iollama/Voice-Assistant-5/personas/Historical/Alexander Hamilton/concerned.jpg

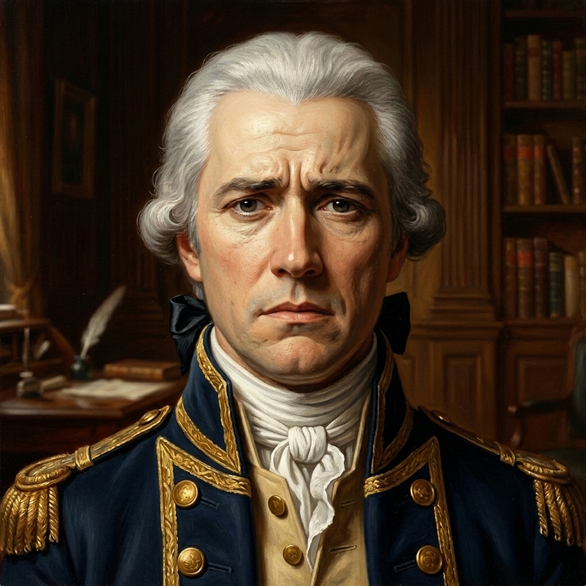
personas/Historical/Alexander Hamilton/concerned.jpg
