iollama/Voice-Assistant-5/personas/Historical/Alexander Hamilton/confused.jpg

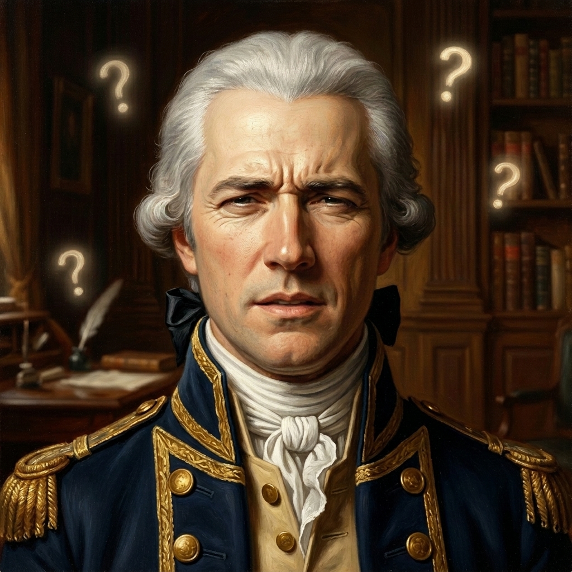
personas/Historical/Alexander Hamilton/confused.jpg
