iollama/Voice-Assistant-5/personas/Historical/Alexander Hamilton/excited.jpg

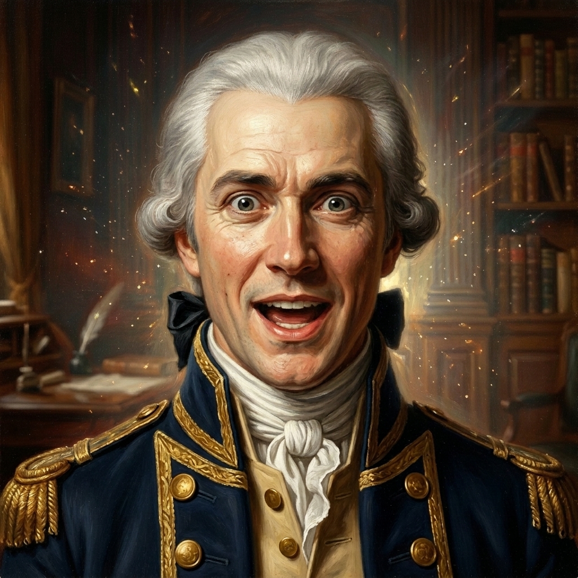
personas/Historical/Alexander Hamilton/excited.jpg
