iollama/Voice-Assistant-5/personas/Historical/Theodor Herzl/concerned.jpg

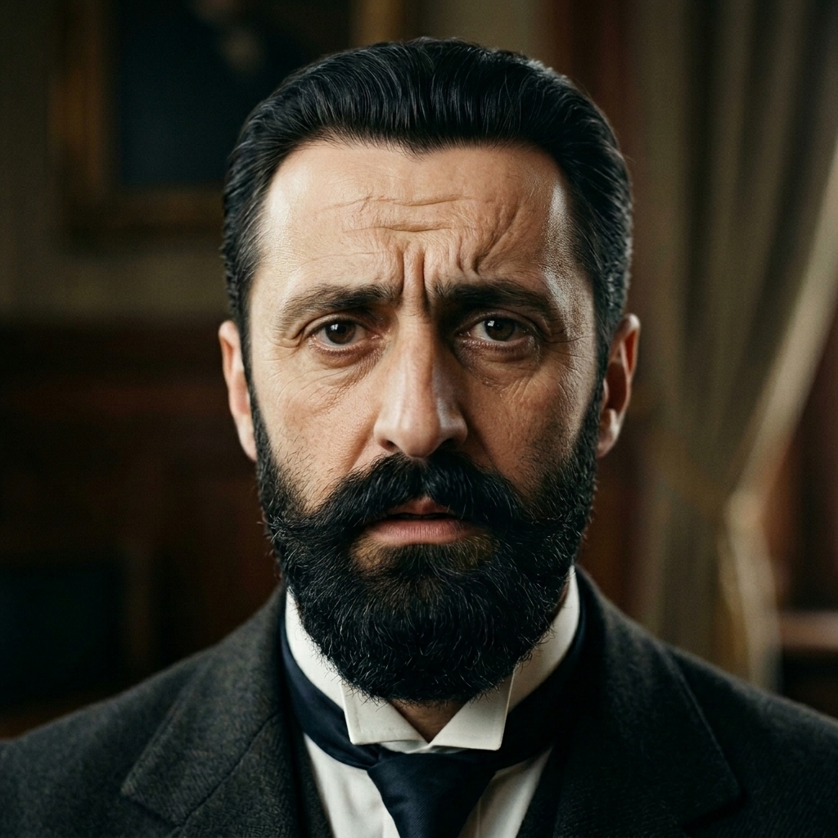
personas/Historical/Theodor Herzl/concerned.jpg
