iollama/Voice-Assistant-5/personas/Historical/Theodor Herzl/confused.jpg

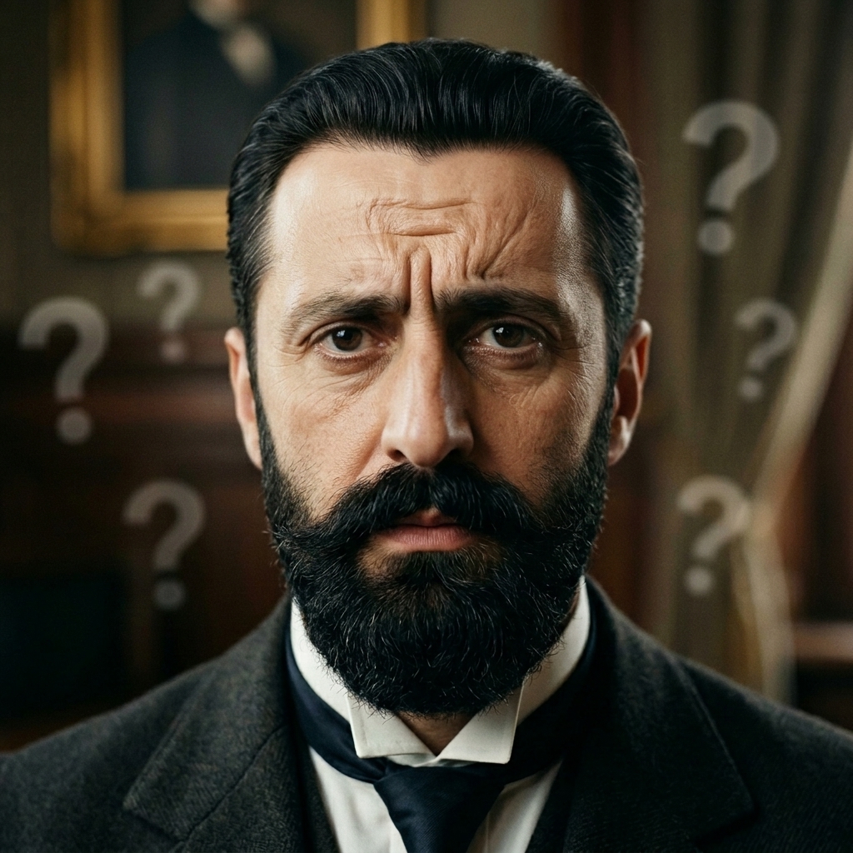
personas/Historical/Theodor Herzl/confused.jpg
