iollama/Voice-Assistant-5/personas/Historical/Theodor Herzl/excited.jpg

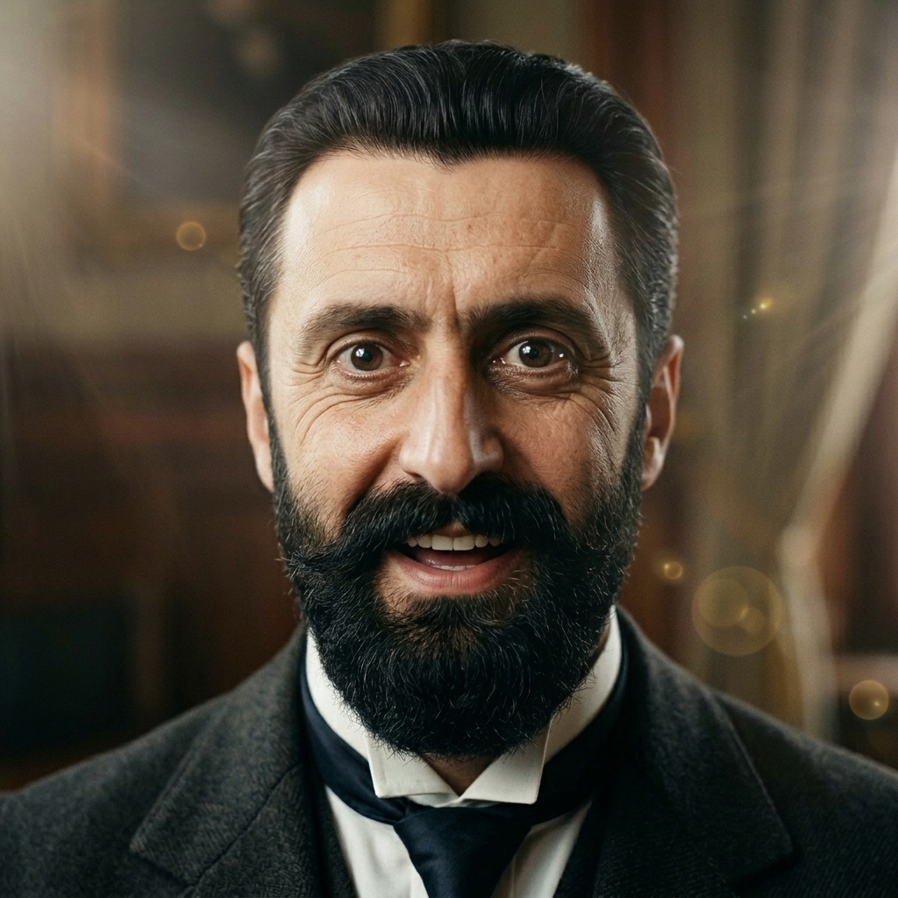
personas/Historical/Theodor Herzl/excited.jpg
