iollama/Voice-Assistant-5/voice_agent_5/utils/preview/confused.gif

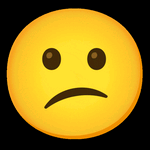
voice_agent_5/utils/preview/confused.gif
