iollama/Voice-Assistant-5/voice_agent_5/utils/preview/empathetic.gif

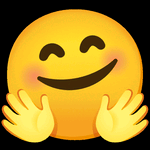
voice_agent_5/utils/preview/empathetic.gif
