iollama/Voice-Assistant-5/voice_agent_5/utils/preview/excited.gif

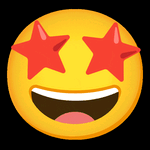
voice_agent_5/utils/preview/excited.gif
