iollama/Voice-Assistant-5/voice_agent_5/utils/preview/neutral.gif

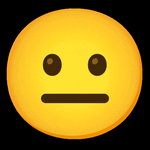
voice_agent_5/utils/preview/neutral.gif
