iollama/Voice-Assistant-5/voice_agent_5/webserver.ino

// =====================================================================
// NVS Config & WebServer Handlers
// =====================================================================

// Reads every persisted setting into RAM. Callable at boot (single-threaded)
// and from /restoreAgent (Core 1, with the protocol task live), so the three
// mutex-protected globals are assigned under agent_config_lock().
void load_agent_config() {
  preferences.begin("agentConfig", true);

  size_t blob_len = preferences.getBytesLength("sysPrompt");
  bool needs_sysprompt_migration = false;
  String loaded_prompt;
  if (blob_len > 0) {
    char* buf = (char*)malloc(blob_len + 1);
    preferences.getBytes("sysPrompt", buf, blob_len);
    buf[blob_len] = '\0';
    loaded_prompt = String(buf);
    free(buf);
  } else {
    String legacy = preferences.getString("sysPrompt", "");
    if (legacy.length() > 0) {
      loaded_prompt = legacy;
      needs_sysprompt_migration = true;
    } else {
      loaded_prompt = DEFAULT_SYS_INSTRUCTION;
    }
  }

  g_temperature = preferences.getFloat("temp", DEFAULT_TEMPERATURE);
  g_persist_conversation = preferences.getBool("persist", DEFAULT_PERSIST_CONVO);
  g_verbose_logging = preferences.getBool("verbose", DEFAULT_VERBOSE_LOGGING);
  g_show_hidden_personas = preferences.getBool("showHidden", DEFAULT_SHOW_HIDDEN);
  g_api_key = preferences.getString("apiKey", "");
  g_volume = preferences.getInt("volume", 50);
  if (g_volume < 0) g_volume = 0;
  if (g_volume > 100) g_volume = 100;
  g_audio_output = preferences.getUChar("audioOut", AUDIO_OUT_SPEAKER);
  if (g_audio_output > AUDIO_OUT_HEADPHONES) g_audio_output = AUDIO_OUT_SPEAKER;
  String loaded_voice = preferences.getString("voice", DEFAULT_VOICE);
  if (!voice_is_allowed(loaded_voice)) {
    CPRINTF("NVS: stored voice '%s' not in whitelist, falling back to '%s'\n",
            loaded_voice.c_str(), DEFAULT_VOICE);
    loaded_voice = DEFAULT_VOICE;
  }
  String loaded_language = preferences.getString("lang", DEFAULT_LANGUAGE);
  if (!language_is_allowed(loaded_language)) {
    CPRINTF("NVS: stored language '%s' not in whitelist, falling back to '%s'\n",
            loaded_language.c_str(), DEFAULT_LANGUAGE);
    loaded_language = DEFAULT_LANGUAGE;
  }
  preferences.end();

  agent_config_lock();
  g_sys_instruction = loaded_prompt;
  g_voice           = loaded_voice;
  g_language        = loaded_language;
  agent_config_unlock();

  if (needs_sysprompt_migration) {
    // The blob has to replace the string under the same key, so the remove
    // comes first — which means a failed putBytes would leave NOTHING stored
    // and the next boot would come up on DEFAULT_SYS_INSTRUCTION. Put the
    // legacy string back rather than losing the user's persona.
    preferences.begin("agentConfig", false);
    preferences.remove("sysPrompt");
    size_t written = preferences.putBytes("sysPrompt", loaded_prompt.c_str(),
                                          loaded_prompt.length());
    bool ok = (written == loaded_prompt.length());
    if (!ok) {
      preferences.remove("sysPrompt");
      bool restored = (preferences.putString("sysPrompt", loaded_prompt) > 0);
      CPRINTF("NVS: sysPrompt migration FAILED (wrote %u of %u bytes) — "
              "NVS is full; legacy string %s\n",
              (unsigned)written, (unsigned)loaded_prompt.length(),
              restored ? "restored, will retry next boot" : "COULD NOT BE RESTORED");
    }
    preferences.end();
    if (ok) {
      CPRINTF("NVS: migrated sysPrompt from string to blob (%u bytes)\n",
              (unsigned)loaded_prompt.length());
    }
  }
}

// Main settings page HTML/CSS/JS lives in root_page.h (static PROGMEM), served
// verbatim. Live values are delivered separately via GET /api/config; saves use
// the existing form-POST handlers below. Kept in a .h for the same reason as
// emojis_page.h (Arduino auto-prototyper chokes on embedded JS in .ino files).
#include "root_page.h"
void handle_root() {
  server.sendHeader("Cache-Control", "no-cache");
  server.send_P(200, "text/html; charset=utf-8", ROOT_PAGE_HTML);
}

// Shared idle gate for portal actions that are slow or disruptive.
// server.handleClient() runs on Core 1 alongside captureMicrophone() and
// manageSpeaker(), so a handler that occupies Core 1 for any length of time
// underruns the speaker DMA or drops mic audio. Every such endpoint refuses with
// HTTP 409 mid-turn. Cheap reads don't need the gate.
static bool assistant_in_turn() {
  AssistantState s = (AssistantState)g_state;
  return s == STATE_RECORDING || s == STATE_THINKING || s == STATE_SPEAKING;
}

// Sends the 409 and returns true when the caller should stop.
static bool reject_if_busy() {
  if (!assistant_in_turn()) return false;
  server.send(409, "text/plain", "Busy - try again after the current response.");
  return true;
}

// Escape a string for safe embedding inside a JSON double-quoted value.
static String json_escape(const String& in) {
  String out;
  out.reserve(in.length() + 8);
  for (size_t i = 0; i < in.length(); i++) {
    char c = in[i];
    switch (c) {
      case '"':  out += "\\\""; break;
      case '\\': out += "\\\\"; break;
      case '\n': out += "\\n";  break;
      case '\r': out += "\\r";  break;
      case '\t': out += "\\t";  break;
      default:
        if ((uint8_t)c < 0x20) {
          char buf[7];
          snprintf(buf, sizeof(buf), "\\u%04x", (unsigned)(uint8_t)c);
          out += buf;
        } else {
          out += c;
        }
    }
  }
  return out;
}

// ---- GET /api/config -------------------------------------------------
// Current settings for the static main page to populate itself with.
// Never returns the API key itself — only whether a custom key is set.
void handle_config() {
  // Snapshot the mutex-protected trio into locals first — never hold the lock
  // across the JSON building below.
  String cfg_prompt, cfg_voice, cfg_language;
  agent_config_snapshot(cfg_prompt, cfg_voice, cfg_language);

  String json = "{";
  json += "\"sysPrompt\":\"" + json_escape(cfg_prompt) + "\",";
  json += "\"voice\":\"" + json_escape(cfg_voice) + "\",";
  json += "\"voices\":[";
  for (size_t i = 0; i < VOICE_OPTIONS_COUNT; ++i) {
    if (i) json += ",";
    json += "{\"id\":\"" + String(VOICE_OPTIONS[i].id) + "\",";
    json += "\"label\":\"" + json_escape(VOICE_OPTIONS[i].label) + "\"}";
  }
  json += "],";
  json += "\"language\":\"" + json_escape(cfg_language) + "\",";
  json += "\"languages\":[";
  for (size_t i = 0; i < LANGUAGE_OPTIONS_COUNT; ++i) {
    if (i) json += ",";
    json += "{\"id\":\"" + String(LANGUAGE_OPTIONS[i].id) + "\",";
    json += "\"label\":\"" + json_escape(LANGUAGE_OPTIONS[i].label) + "\"}";
  }
  json += "],";
  json += "\"persist\":"  + String(g_persist_conversation ? "true" : "false") + ",";
  json += "\"verbose\":"  + String(g_verbose_logging ? "true" : "false") + ",";
  json += "\"showHidden\":" + String(g_show_hidden_personas ? "true" : "false") + ",";
  json += "\"volume\":"   + String((int)g_volume) + ",";
  json += "\"audioOut\":" + String((int)g_audio_output) + ",";
  // LittleFS storage budget — the portal's "Provision default persona" preflight checks
  // the decoded frame total against fsFree before writing anything to /default.
  json += "\"fsTotal\":" + String((uint32_t)LittleFS.totalBytes()) + ",";
  json += "\"fsFree\":"  + String((uint32_t)(LittleFS.totalBytes() - LittleFS.usedBytes())) + ",";
  json += "\"apiKeySet\":" + String(g_api_key.length() > 0 ? "true" : "false") + ",";
  json += "\"apMode\":"   + String(ap_mode ? "true" : "false") + ",";
  json += "\"ssid\":\""   + json_escape(ap_mode ? WiFi.softAPSSID() : WiFi.SSID()) + "\",";
#if USE_DISPLAY
  json += "\"useDisplay\":true,";
#else
  json += "\"useDisplay\":false,";
#endif
  json += "\"tokens\":{";
  json += "\"total\":"       + String((uint32_t)g_tokens.total);
  json += ",\"input\":"      + String((uint32_t)g_tokens.input);
  json += ",\"inputCached\":" + String((uint32_t)g_tokens.input_cached);
  json += ",\"inputText\":"  + String((uint32_t)g_tokens.input_text);
  json += ",\"inputAudio\":" + String((uint32_t)g_tokens.input_audio);
  json += ",\"output\":"     + String((uint32_t)g_tokens.output);
  json += ",\"outputText\":" + String((uint32_t)g_tokens.output_text);
  json += ",\"outputAudio\":" + String((uint32_t)g_tokens.output_audio);
  json += "}}";
  server.sendHeader("Cache-Control", "no-cache");
  server.send(200, "application/json", json);
}

// =====================================================================
// WI-FI NETWORK API
// =====================================================================
// Up to WIFI_MAX_NETWORKS saved networks; the store itself lives in wifi_store.h
// and is persisted by wifi_store_persist() in wifi.ino.
//
// NO ROUTE HERE EVER RETURNS A STORED PASSWORD. Passwords go in and are never
// readable back out — that property is what makes the (currently plaintext) NVS
// blob acceptable, and it must survive any change to these handlers.

// wifi_store_remove() compacts the array, so a cached slot index goes stale after
// any deletion. Re-derive it from the SSID we are actually associated with.
static void wifi_refresh_active_slot() {
  g_wifi_active_slot = ap_mode ? -1 : wifi_store_find(g_wifi_store, WiFi.SSID().c_str());
}

// Saved networks, most recently used first — the same order the boot cascade tries.
static String wifi_nets_json() {
  String json = "{";
  json += "\"max\":"    + String(WIFI_MAX_NETWORKS) + ",";
  json += "\"count\":"  + String((int)g_wifi_store.count) + ",";
  json += "\"apMode\":" + String(ap_mode ? "true" : "false") + ",";
  json += "\"nets\":[";
  uint8_t order[WIFI_MAX_NETWORKS];
  int n = wifi_store_order_by_recency(g_wifi_store, order);
  for (int i = 0; i < n; i++) {
    const WifiNet& net = g_wifi_store.nets[order[i]];
    if (i) json += ",";
    json += "{\"ssid\":\""   + json_escape(net.ssid) + "\"";
    json += ",\"lastUsed\":"  + String((uint32_t)net.last_epoch);
    json += ",\"neverUsed\":" + String(net.use_seq == 0 ? "true" : "false");
    json += ",\"active\":"    + String((!ap_mode && (int)order[i] == g_wifi_active_slot)
                                       ? "true" : "false");
    json += "}";
  }
  json += "],";
  // Outcome of an explicit Connect request, if one was made before this boot. The
  // page uses it to report a target it could not reach, since the reboot destroys
  // the request's own HTTP response.
  json += "\"lastAttempt\":";
  if (g_wifi_request_ssid.length() > 0) {
    json += "{\"ssid\":\"" + json_escape(g_wifi_request_ssid) + "\",\"ok\":";
    json += g_wifi_request_ok ? "true" : "false";
    json += "}";
  } else {
    json += "null";
  }
  json += "}";
  return json;
}

// ---- GET /api/wifi ---------------------------------------------------
void handle_wifi_list() {
  server.sendHeader("Cache-Control", "no-cache");
  server.send(200, "application/json", wifi_nets_json());
}

// ---- GET /api/wifi/scan ----------------------------------------------
// Asynchronous by necessity. WiFi.scanNetworks() blocks for 2-4 s, and this
// handler runs on Core 1 inside server.handleClient() — blocking there would
// starve the audio loop. So: the first call kicks off a background scan and
// answers {"status":"scanning"}; the page polls until the results are ready.
// The boot cascade is the one place a blocking scan is legitimate, because it
// runs in setup() before loop() and the protocol task exist.
void handle_wifi_scan() {
  if (reject_if_busy()) return;

  // Tracks whether the poll sequence we are in has already started a scan, so a
  // fresh press of Scan never answers with leftovers from an abandoned earlier
  // one. (A request abandoned mid-scan can still yield one stale list on the next
  // press; harmless, since saving a network that is not currently in range is a
  // supported action anyway.)
  static bool scan_started = false;

  int16_t n = WiFi.scanComplete();

  if (!scan_started) {
    if (n >= 0) WiFi.scanDelete();     // discard results nobody collected
    WiFi.scanNetworks(true);
    scan_started = true;
    server.send(200, "application/json", "{\"status\":\"scanning\"}");
    return;
  }
  if (n == WIFI_SCAN_RUNNING) {
    server.send(200, "application/json", "{\"status\":\"scanning\"}");
    return;
  }
  if (n < 0) {
    scan_started = false;              // let the next press try again
    server.send(500, "text/plain", "Scan failed");
    return;
  }

  const int SCAN_MAX = 64;
  if (n > SCAN_MAX) n = SCAN_MAX;

  // Sort indices by RSSI descending, so the dedup below keeps the strongest BSSID
  // for each SSID and the page lists the nearest networks first.
  int idx[SCAN_MAX];
  for (int i = 0; i < n; i++) idx[i] = i;
  for (int i = 1; i < n; i++) {
    int key = idx[i];
    int j = i - 1;
    while (j >= 0 && WiFi.RSSI(idx[j]) < WiFi.RSSI(key)) { idx[j + 1] = idx[j]; j--; }
    idx[j + 1] = key;
  }

  // Pull each SSID out once. WiFi.SSID(int) builds a String per call, and the
  // dedup below is O(n^2) — calling it inside the inner loop would mean up to
  // ~2000 transient heap allocations on Core 1, which is the churn the
  // no-heap-on-the-audio-path rule exists to avoid even though this is off it.
  String ssids[SCAN_MAX];
  for (int i = 0; i < n; i++) ssids[i] = WiFi.SSID(idx[i]);

  String json = "{\"status\":\"done\",\"nets\":[";
  int emitted = 0;
  for (int i = 0; i < n; i++) {
    const String& ssid = ssids[i];
    if (ssid.length() == 0) continue;   // hidden SSID — nothing to offer the user
    bool dup = false;
    for (int j = 0; j < i; j++) {
      if (ssids[j] == ssid) { dup = true; break; }   // sorted by RSSI, so [j] is the stronger
    }
    if (dup) continue;
    if (emitted) json += ",";
    json += "{\"ssid\":\"" + json_escape(ssid) + "\"";
    json += ",\"rssi\":"   + String((int)WiFi.RSSI(idx[i]));
    json += ",\"secure\":" + String(WiFi.encryptionType(idx[i]) != WIFI_AUTH_OPEN
                                    ? "true" : "false");
    json += ",\"saved\":"  + String(wifi_store_find(g_wifi_store, ssid.c_str()) >= 0
                                    ? "true" : "false");
    json += "}";
    emitted++;
  }
  json += "]}";

  WiFi.scanDelete();
  scan_started = false;
  server.sendHeader("Cache-Control", "no-cache");
  server.send(200, "application/json", json);
}

// ---- POST /api/wifi/add ----------------------------------------------
// Adds a network, or replaces the password of one already saved. No reboot and
// no change to the current connection — pre-loading a network you are nowhere
// near is the point. The response says exactly what happened (including which
// entry was evicted to make room) so the page can report it.
void handle_wifi_add() {
  if (reject_if_busy()) return;

  String ssid = server.arg("ssid");
  String pass = server.arg("pass");
  if (ssid.length() == 0) {
    server.send(400, "text/plain", "SSID required");
    return;
  }
  if (ssid.length() >= WIFI_SSID_MAX) {
    server.send(400, "text/plain", "SSID too long (max 32 characters)");
    return;
  }
  if (pass.length() >= WIFI_PASS_MAX) {
    server.send(400, "text/plain", "Password too long (max 63 characters)");
    return;
  }

  bool updated = wifi_store_find(g_wifi_store, ssid.c_str()) >= 0;
  char evicted[WIFI_SSID_MAX];
  int slot = wifi_store_upsert(g_wifi_store, ssid.c_str(), pass.c_str(), evicted);
  if (slot < 0) {
    server.send(400, "text/plain", "Could not save that network");
    return;
  }
  if (!wifi_store_persist()) {
    server.send(500, "text/plain",
                "Settings storage is full — the network was not saved.");
    return;
  }
  wifi_refresh_active_slot();

  CPRINTF("Wi-Fi store: %s '%s' in slot %d%s%s\n",
          updated ? "updated" : "added", ssid.c_str(), slot,
          evicted[0] ? ", evicted " : "", evicted[0] ? evicted : "");

  String json = "{\"ok\":true,\"ssid\":\"" + json_escape(ssid) + "\"";
  json += ",\"updated\":" + String(updated ? "true" : "false");
  json += ",\"count\":"   + String((int)g_wifi_store.count);
  json += ",\"evicted\":";
  if (evicted[0]) {
    json += "\"";
    json += json_escape(evicted);
    json += "\"";
  } else {
    json += "null";
  }
  json += "}";
  server.send(200, "application/json", json);
}

// ---- POST /api/wifi/delete -------------------------------------------
// Forgets a saved network. Deleting the one currently in use does NOT drop the
// link — it only means the next boot won't choose it.
void handle_wifi_delete() {
  if (reject_if_busy()) return;

  String ssid = server.arg("ssid");
  if (!wifi_store_remove(g_wifi_store, ssid.c_str())) {
    server.send(404, "text/plain", "No saved network with that name");
    return;
  }
  if (!wifi_store_persist()) {
    server.send(500, "text/plain",
                "Settings storage is full — the network was not forgotten and "
                "will come back after a reboot.");
    return;
  }
  wifi_refresh_active_slot();
  CPRINTF("Wi-Fi store: forgot '%s' (%u left)\n", ssid.c_str(), (unsigned)g_wifi_store.count);

  String json = "{\"ok\":true,\"ssid\":\"" + json_escape(ssid) + "\"";
  json += ",\"count\":" + String((int)g_wifi_store.count) + "}";
  server.send(200, "application/json", json);
}

// ---- POST /api/wifi/connect ------------------------------------------
// Switch to a saved network: record it as the next boot's target, mark it
// most-recently-used, and reboot. Rebooting rather than re-associating in place is
// deliberate — a failed in-place switch would strand the device with neither a
// station link nor a portal, whereas the cascade falls through to the next
// candidate and ultimately to the captive portal on its own.
//
// The pending target is what makes the request stick. Recency alone is not enough:
// it only sets the *order* of the candidate list, and the candidate list is built
// from a scan, so a target the scan happens to miss would be dropped and the device
// would silently rejoin the network you just asked it to leave. The boot cascade
// attempts a pending target directly, before it scans at all.
void handle_wifi_connect() {
  if (reject_if_busy()) return;

  String ssid = server.arg("ssid");
  int idx = wifi_store_find(g_wifi_store, ssid.c_str());
  if (idx < 0) {
    server.send(404, "text/plain", "No saved network with that name");
    return;
  }
  wifi_store_mark_used(g_wifi_store, idx, 0);
  wifi_store_persist();  // best-effort: recency only, the pending target below is what switches
  if (!wifi_set_pending_target(ssid.c_str())) {
    // Rebooting now would silently rejoin the network the user asked to leave.
    server.send(500, "text/plain",
                "Settings storage is full — could not pin the target network, "
                "so the device was not restarted.");
    return;
  }
  CPRINTF("Wi-Fi store: '%s' pinned as the next boot target; restarting to connect\n",
          ssid.c_str());

  server.send(200, "application/json", "{\"ok\":true,\"rebooting\":true}");
  delay(500);
  ESP.restart();
}
// Personality card: system prompt + voice only. persist/verbose moved to the
// admin Behavior card (handle_save_behavior) so saving the prompt can't clear
// the checkbox-backed flags.
// Persist first, update RAM only on success. GET /api/config serves the RAM
// globals, so updating them for a write that didn't land makes the portal show
// a persona the next boot won't have — which is exactly how a full NVS used to
// masquerade as a successful save. A partial write reports 500 and leaves the
// pieces that failed untouched; postForm() in portal_js.h turns that into a
// visible error in the import summary.
void handle_save_agent() {
  if (reject_if_busy()) return;  // ~12 KB blob rewrite erases ~8 flash pages on Core 1

  String submitted_prompt = server.arg("sysPrompt");
  if (submitted_prompt.length() > 12288) {
    server.send(413, "text/plain", "System prompt too large (max 12 KB)");
    return;
  }
  preferences.begin("agentConfig", false);

  size_t written = preferences.putBytes("sysPrompt", submitted_prompt.c_str(),
                                        submitted_prompt.length());
  bool prompt_ok = (written == submitted_prompt.length());
  if (!prompt_ok) {
    CPRINTF("POST /saveAgent: sysPrompt write FAILED (%u of %u bytes) — "
            "NVS full\n",
            (unsigned)written, (unsigned)submitted_prompt.length());
  }

  String submitted_voice = server.arg("voice");
  bool voice_ok = true, voice_present = false;
  if (voice_is_allowed(submitted_voice)) {
    voice_present = true;
    voice_ok = (preferences.putString("voice", submitted_voice) > 0);
    if (!voice_ok) CPRINTLN("POST /saveAgent: voice write FAILED — NVS full");
  } else if (submitted_voice.length() > 0) {
    CPRINTF("POST /saveAgent: voice '%s' not in whitelist, ignored\n",
            submitted_voice.c_str());
  }

  String submitted_language = server.arg("language");
  bool lang_ok = true, lang_present = false;
  if (language_is_allowed(submitted_language)) {
    lang_present = true;
    lang_ok = (preferences.putString("lang", submitted_language) > 0);
    if (!lang_ok) CPRINTLN("POST /saveAgent: language write FAILED — NVS full");
  } else if (submitted_language.length() > 0) {
    CPRINTF("POST /saveAgent: language '%s' not in whitelist, ignored\n",
            submitted_language.c_str());
  }
  preferences.end();

  // Adopt only what actually persisted.
  agent_config_lock();
  if (prompt_ok)                  g_sys_instruction = submitted_prompt;
  if (voice_present && voice_ok)  g_voice           = submitted_voice;
  if (lang_present && lang_ok)    g_language        = submitted_language;
  agent_config_unlock();

  if (prompt_ok || (voice_present && voice_ok) || (lang_present && lang_ok)) {
    g_reconnect_pending = true;  // re-apply persona/voice/language to the live session
  }

  if (!prompt_ok || !voice_ok || !lang_ok) {
    String failed;
    if (!prompt_ok) failed += "persona ";
    if (!voice_ok)  failed += "voice ";
    if (!lang_ok)   failed += "language ";
    failed.trim();
    server.send(500, "text/plain",
                "Settings storage is full — could not save: " + failed +
                ". Try Admin Zone -> Restore Defaults, then re-import.");
    return;
  }

  server.sendHeader("Location", "/", true);
  server.send(302, "text/plain", "");
}

// Admin Behavior card: persist conversation + verbose logging + show-hidden-personas.
void handle_save_behavior() {
  preferences.begin("agentConfig", false);
  g_persist_conversation = server.hasArg("persist");
  g_verbose_logging = server.hasArg("verbose");
  g_show_hidden_personas = server.hasArg("showHidden");
  preferences.putBool("persist", g_persist_conversation);
  preferences.putBool("verbose", g_verbose_logging);
  preferences.putBool("showHidden", g_show_hidden_personas);
  preferences.end();
  server.sendHeader("Location", "/", true);
  server.send(302, "text/plain", "");
}
void handle_restore_agent() {
  preferences.begin("agentConfig", false);
  preferences.clear();
  preferences.end();
  load_agent_config();
  g_reconnect_pending = true;  // re-apply restored defaults to the live session
  server.sendHeader("Location", "/", true);
  server.send(302, "text/plain", "");
}
void handle_save_api_key() {
  String key = server.arg("apiKey");
  if (key.length() > 0) {
    preferences.begin("agentConfig", false);
    bool ok = (preferences.putString("apiKey", key) > 0);
    preferences.end();
    if (!ok) {
      // Same trap as the persona: adopting it in RAM would look like a save
      // that survives a reboot, and it wouldn't.
      CPRINTLN("POST /saveApiKey: write FAILED — NVS full");
      server.send(500, "text/plain",
                  "Settings storage is full — the API key was not saved.");
      return;
    }
    g_api_key = key;
  }
  server.sendHeader("Location", "/", true);
  server.send(302, "text/plain", "");
}
void handle_clear_api_key() {
  preferences.begin("agentConfig", false);
  preferences.remove("apiKey");
  preferences.end();
  g_api_key = "";
  server.sendHeader("Location", "/", true);
  server.send(302, "text/plain", "");
}
void handle_save_volume() {
  g_volume = server.arg("volume").toInt();
  preferences.begin("agentConfig", false);
  preferences.putInt("volume", g_volume);
  preferences.end();
  server.sendHeader("Location", "/", true);
  server.send(302, "text/plain", "");
}

void handle_save_audio_out() {
  // Reject mid-conversation — flipping mute pins while audio is flowing
  // would cause a pop and disrupt the turn. Same idle gate as emoji uploads
  // and the Wi-Fi endpoints.
  if (reject_if_busy()) return;
  String v = server.arg("audioOut");
  uint8_t newOut = (v == "1" || v == "headphones") ? AUDIO_OUT_HEADPHONES : AUDIO_OUT_SPEAKER;
  if (newOut != g_audio_output) {
    g_audio_output = newOut;
    preferences.begin("agentConfig", false);
    preferences.putUChar("audioOut", g_audio_output);
    preferences.end();
    apply_audio_output();
  }
  server.sendHeader("Location", "/", true);
  server.send(302, "text/plain", "");
}

// =====================================================================
// EMOJI WEB API — see plans/so-this-is-jsut-velvety-puffin.md
// =====================================================================
#if USE_DISPLAY

static const char* EMOJI_CUSTOM_DIR  = "/custom";
static const char* EMOJI_STAGE_DIR   = "/custom_stage";
// Provisioning the read-only /default/ set from the web (Admin Zone "Provision default
// persona") is the ONE sanctioned runtime writer of /default/. Every other emoji write
// path touches /custom/ only -- that is what makes Reset un-brickable.
// It reuses the same staged+atomic upload path as /custom/, just with these dirs.
static const char* EMOJI_DEFAULT_DIR       = "/default";
static const char* EMOJI_DEFAULT_STAGE_DIR = "/default_stage";

static int emoji_find_emotion_index(const String& name) {
  for (int e = 0; e < EMOTION_COUNT; e++) {
    if (name == EMOTION_NAMES[e]) return e;
  }
  return -1;
}

// Resolve the directory currently serving frames for an emotion.
static const char* emoji_source_dir_for(uint8_t emotion) {
  char path[EMOJI_PATH_MAX];
  snprintf(path, sizeof(path), "/custom/%s_0.bin", EMOTION_NAMES[emotion]);
  return LittleFS.exists(path) ? "/custom" : "/default";
}

// Remove every frame file for one emotion from a given directory (custom, default, or a stage).
static void emoji_delete_set_in(const char* dir, uint8_t emotion) {
  char path[EMOJI_PATH_MAX];
  for (int i = 0; i < EMOJI_NUM_FRAMES; i++) {
    snprintf(path, sizeof(path), "%s/%s_%d.bin", dir, EMOTION_NAMES[emotion], i);
    LittleFS.remove(path);
  }
}

static void emoji_delete_custom_files(uint8_t emotion) { emoji_delete_set_in(EMOJI_CUSTOM_DIR, emotion); }
static void emoji_cleanup_stage_for(uint8_t emotion)   { emoji_delete_set_in(EMOJI_STAGE_DIR, emotion); }

// ---- GET /api/emoji/manifest ----------------------------------------
// Returns { "<emotion>": {"count": N, "source": "default"|"custom"}, ... }
void handle_emoji_manifest() {
  String json = "{";
  for (int e = 0; e < EMOTION_COUNT; e++) {
    if (e > 0) json += ",";
    const char* src = emoji_source_dir_for(e);
    const char* src_label = (strcmp(src, "/custom") == 0) ? "custom" : "default";
    json += "\""; json += EMOTION_NAMES[e]; json += "\":{";
    json += "\"count\":"; json += String((unsigned)g_frame_counts[e]);
    json += ",\"source\":\""; json += src_label; json += "\"}";
  }
  json += "}";
  server.sendHeader("Cache-Control", "no-cache");
  server.send(200, "application/json", json);
}

// ---- GET /api/emoji/<emotion>/<n>.bin -------------------------------
void handle_emoji_get_frame(const String& uri) {
  int slash = uri.indexOf('/', 11);   // first slash after "/api/emoji/"
  if (slash < 0) { server.send(404, "text/plain", "bad path"); return; }
  String name = uri.substring(11, slash);
  int e = emoji_find_emotion_index(name);
  if (e < 0) { server.send(404, "text/plain", "unknown emotion"); return; }

  String tail = uri.substring(slash + 1);
  if (!tail.endsWith(".bin")) { server.send(404, "text/plain", "bad path"); return; }
  int idx = tail.substring(0, tail.length() - 4).toInt();
  if (idx < 0 || idx >= EMOJI_NUM_FRAMES) { server.send(404, "text/plain", "bad index"); return; }

  char path[EMOJI_PATH_MAX];
  snprintf(path, sizeof(path), "%s/%s_%d.bin", emoji_source_dir_for((uint8_t)e), name.c_str(), idx);
  File f = LittleFS.open(path, "r");
  if (!f) { server.send(404, "text/plain", "not found"); return; }
  server.sendHeader("Cache-Control", "no-cache");
  server.streamFile(f, "application/octet-stream");
  f.close();
}

// ---- POST /api/emoji/<emotion>/reset --------------------------------
void handle_emoji_reset(uint8_t emotion) {
  if (assistant_in_turn()) {
    server.send(409, "text/plain", "Busy - try again after the current response.");
    return;
  }
  emoji_delete_custom_files(emotion);
  emoji_rescan_frame_counts();
  g_loaded_emotion = 0xFF;
  server.send(200, "application/json", "{\"ok\":true}");
}

// ---- POST /api/emoji/reset-all --------------------------------------
void handle_emoji_reset_all() {
  if (assistant_in_turn()) {
    server.send(409, "text/plain", "Busy - try again after the current response.");
    return;
  }
  for (int e = 0; e < EMOTION_COUNT; e++) emoji_delete_custom_files((uint8_t)e);
  emoji_rescan_frame_counts();
  g_loaded_emotion = 0xFF;
  server.send(200, "application/json", "{\"ok\":true}");
}

// ---- POST /api/emoji/<emotion>  and  POST /api/default-emoji/<emotion> ----
// Multipart with single file field. Body bytes are N x EMOJI_FRAME_BYTES, N in 1..8.
// Slices on-the-fly into <stage_dir>/<emotion>_<i>.bin during streaming, then atomically
// renames the whole set into <final_dir> on success. The route picks the target dirs:
//   /api/emoji/...          -> /custom_stage -> /custom   (user override)
//   /api/default-emoji/...  -> /default_stage -> /default (web provisioning; see invariants)
struct EmojiUploadState {
  int   emotion;
  File  f;
  int   frame_idx;
  size_t frame_bytes;
  size_t total_bytes;
  bool  failed;
  int   http_status;
  String error_msg;
  const char* stage_dir;
  const char* final_dir;
};
static EmojiUploadState g_eu = {-1, File(), 0, 0, 0, false, 200, "", EMOJI_STAGE_DIR, EMOJI_CUSTOM_DIR};

static void eu_fail(int status, const char* msg) {
  if (g_eu.failed) return;
  g_eu.failed = true;
  g_eu.http_status = status;
  g_eu.error_msg = msg;
}

void handle_emoji_replace_chunk() {
  HTTPUpload& upload = server.upload();

  if (upload.status == UPLOAD_FILE_START) {
    // Reset state for the new multipart file
    g_eu.frame_idx = 0;
    g_eu.frame_bytes = 0;
    g_eu.total_bytes = 0;
    g_eu.failed = false;
    g_eu.http_status = 200;
    g_eu.error_msg = "";
    g_eu.stage_dir = EMOJI_STAGE_DIR;   // safe defaults (used by cleanup if we fail early)
    g_eu.final_dir = EMOJI_CUSTOM_DIR;
    if (g_eu.f) g_eu.f.close();

    if (g_emoji_upload_active) {
      eu_fail(409, "Another upload in progress");
      return;
    }
    g_emoji_upload_active = true;

    if (assistant_in_turn()) {
      eu_fail(409, "Busy - try again after the current response.");
      return;
    }

    // Pick the target overlay from the route prefix. /default/ is the sanctioned
    // web-provisioning path (Admin Zone); everything else is the user /custom/ override.
    String uri = server.uri();
    String name;
    if (uri.startsWith("/api/default-emoji/")) {
      g_eu.stage_dir = EMOJI_DEFAULT_STAGE_DIR;
      g_eu.final_dir = EMOJI_DEFAULT_DIR;
      name = uri.substring(19);
    } else if (uri.startsWith("/api/emoji/")) {
      g_eu.stage_dir = EMOJI_STAGE_DIR;
      g_eu.final_dir = EMOJI_CUSTOM_DIR;
      name = uri.substring(11);
    } else { eu_fail(404, "Bad path"); return; }
    int e = emoji_find_emotion_index(name);
    if (e < 0) { eu_fail(404, "Unknown emotion"); return; }
    g_eu.emotion = e;

    size_t free_bytes = LittleFS.totalBytes() - LittleFS.usedBytes();
    if (free_bytes < (size_t)EMOJI_FRAME_BYTES * EMOJI_NUM_FRAMES + 4096) {
      eu_fail(507, "Insufficient storage");
      return;
    }

    LittleFS.mkdir(g_eu.stage_dir);

    char path[EMOJI_PATH_MAX];
    snprintf(path, sizeof(path), "%s/%s_0.bin", g_eu.stage_dir, EMOTION_NAMES[e]);
    g_eu.f = LittleFS.open(path, "w");
    if (!g_eu.f) { eu_fail(500, "Open staging failed"); return; }

  } else if (upload.status == UPLOAD_FILE_WRITE) {
    if (g_eu.failed) return;
    const uint8_t* data = upload.buf;
    size_t remaining = upload.currentSize;
    while (remaining > 0) {
      if (g_eu.frame_bytes == (size_t)EMOJI_FRAME_BYTES) {
        g_eu.f.close();
        g_eu.frame_idx++;
        g_eu.frame_bytes = 0;
        if (g_eu.frame_idx >= EMOJI_NUM_FRAMES) { eu_fail(400, "Too many frames"); return; }
        char path[EMOJI_PATH_MAX];
        snprintf(path, sizeof(path), "%s/%s_%d.bin",
                 g_eu.stage_dir, EMOTION_NAMES[g_eu.emotion], g_eu.frame_idx);
        g_eu.f = LittleFS.open(path, "w");
        if (!g_eu.f) { eu_fail(500, "Open staging failed"); return; }
      }
      size_t room = (size_t)EMOJI_FRAME_BYTES - g_eu.frame_bytes;
      size_t to_write = remaining < room ? remaining : room;
      size_t wrote = g_eu.f.write(data, to_write);
      if (wrote != to_write) { eu_fail(507, "Write failed"); return; }
      g_eu.frame_bytes += wrote;
      g_eu.total_bytes += wrote;
      data += wrote;
      remaining -= wrote;
    }

  } else if (upload.status == UPLOAD_FILE_END) {
    if (g_eu.f) g_eu.f.close();

  } else if (upload.status == UPLOAD_FILE_ABORTED) {
    if (g_eu.f) g_eu.f.close();
    eu_fail(400, "Upload aborted");
  }
}

void handle_emoji_replace_done() {
  if (!g_emoji_upload_active || g_eu.emotion < 0) {
    server.send(400, "text/plain", "No upload data");
    return;
  }

  if (g_eu.failed) {
    if (g_eu.emotion >= 0) emoji_delete_set_in(g_eu.stage_dir, (uint8_t)g_eu.emotion);
    server.send(g_eu.http_status,
                "text/plain",
                g_eu.error_msg.length() ? g_eu.error_msg : String("Upload failed"));
    g_emoji_upload_active = false;
    return;
  }

  if (g_eu.total_bytes == 0 || (g_eu.total_bytes % EMOJI_FRAME_BYTES) != 0) {
    emoji_delete_set_in(g_eu.stage_dir, (uint8_t)g_eu.emotion);
    server.send(400, "text/plain", "Upload size must be a multiple of 45000 bytes");
    g_emoji_upload_active = false;
    return;
  }
  int new_count = g_eu.total_bytes / EMOJI_FRAME_BYTES;
  if (new_count < 1 || new_count > EMOJI_NUM_FRAMES) {
    emoji_delete_set_in(g_eu.stage_dir, (uint8_t)g_eu.emotion);
    server.send(400, "text/plain", "Bad frame count");
    g_emoji_upload_active = false;
    return;
  }

  LittleFS.mkdir(g_eu.final_dir);
  emoji_delete_set_in(g_eu.final_dir, (uint8_t)g_eu.emotion);

  char src[EMOJI_PATH_MAX], dst[EMOJI_PATH_MAX];
  const char* name = EMOTION_NAMES[g_eu.emotion];
  for (int i = 0; i < new_count; i++) {
    snprintf(src, sizeof(src), "%s/%s_%d.bin", g_eu.stage_dir, name, i);
    snprintf(dst, sizeof(dst), "%s/%s_%d.bin", g_eu.final_dir, name, i);
    if (!LittleFS.rename(src, dst)) {
      CPRINTF("Emoji commit: rename %s -> %s failed\n", src, dst);
    }
  }
  // remove any leftover staging files for higher indices (shouldn't exist but be safe)
  for (int i = new_count; i < EMOJI_NUM_FRAMES; i++) {
    snprintf(src, sizeof(src), "%s/%s_%d.bin", g_eu.stage_dir, name, i);
    LittleFS.remove(src);
  }

  g_frame_counts[g_eu.emotion] = (uint8_t)new_count;
  g_loaded_emotion = 0xFF;

  CPRINTF("Emoji replaced: %s (%d frames)\n", name, new_count);
  String resp = "{\"ok\":true,\"emotion\":\"";
  resp += name;
  resp += "\",\"count\":";
  resp += String(new_count);
  resp += "}";
  server.send(200, "application/json", resp);
  g_emoji_upload_active = false;
}

// ---- GET /emojis  ---------------------------------------------------
// Page HTML+JS lives in emojis_page.h to bypass the Arduino auto-prototyper,
// which mis-parses `async function` inside the raw string as C++ prototypes.
#include "emojis_page.h"
void handle_emojis_page() {
  server.sendHeader("Cache-Control", "no-cache");
  server.send_P(200, "text/html; charset=utf-8", EMOJIS_PAGE_HTML);
}

#endif // USE_DISPLAY

// =====================================================================
// catch-all dispatcher (also handles emoji API)
// =====================================================================
void handle_not_found() {
#if USE_DISPLAY
  String uri = server.uri();
  if (uri.startsWith("/api/emoji/")) {
    if (server.method() == HTTP_GET) {
      if (uri == "/api/emoji/manifest") { handle_emoji_manifest(); return; }
      handle_emoji_get_frame(uri); return;
    } else if (server.method() == HTTP_POST) {
      if (uri == "/api/emoji/reset-all") { handle_emoji_reset_all(); return; }
      if (uri.endsWith("/reset")) {
        String name = uri.substring(11, uri.length() - 6);
        int e = emoji_find_emotion_index(name);
        if (e >= 0) { handle_emoji_reset((uint8_t)e); return; }
      }
    }
    server.send(404, "text/plain", "emoji api: not found");
    return;
  }
#endif
  if (ap_mode) {
    server.send(302, "text/plain", "http://" + WiFi.softAPIP().toString());
  } else {
    server.send(404, "text/plain", "Not Found");
  }
}

void setup_web_server() {
#if USE_DISPLAY
  display_boot_status("Opening the front door");
#endif
  server.on("/", HTTP_GET, handle_root);
  server.on("/api/config", HTTP_GET, handle_config);
  // Saved Wi-Fi networks. These replace the old single-credential /save and
  // /delete form posts.
  server.on("/api/wifi", HTTP_GET, handle_wifi_list);
  server.on("/api/wifi/scan", HTTP_GET, handle_wifi_scan);
  server.on("/api/wifi/add", HTTP_POST, handle_wifi_add);
  server.on("/api/wifi/delete", HTTP_POST, handle_wifi_delete);
  server.on("/api/wifi/connect", HTTP_POST, handle_wifi_connect);
  server.on("/saveAgent", HTTP_POST, handle_save_agent);
  server.on("/saveBehavior", HTTP_POST, handle_save_behavior);
  server.on("/restoreAgent", HTTP_POST, handle_restore_agent);
  server.on("/saveApiKey", HTTP_POST, handle_save_api_key);
  server.on("/clearApiKey", HTTP_POST, handle_clear_api_key);
  server.on("/saveVolume", HTTP_POST, handle_save_volume);
  server.on("/saveAudioOut", HTTP_POST, handle_save_audio_out);

#if USE_DISPLAY
  server.on("/emojis", HTTP_GET, handle_emojis_page);
  // Register the per-emotion emoji upload routes (need an upload callback). The same
  // handlers serve both overlays; the route prefix selects /custom/ vs /default/.
  //   /api/emoji/<emotion>         -> user override (/custom)
  //   /api/default-emoji/<emotion> -> web provisioning of the read-only /default set
  for (int e = 0; e < EMOTION_COUNT; e++) {
    String custom_path  = String("/api/emoji/") + EMOTION_NAMES[e];
    String default_path = String("/api/default-emoji/") + EMOTION_NAMES[e];
    server.on(custom_path,  HTTP_POST, handle_emoji_replace_done, handle_emoji_replace_chunk);
    server.on(default_path, HTTP_POST, handle_emoji_replace_done, handle_emoji_replace_chunk);
  }
#endif

  server.onNotFound(handle_not_found);
  server.begin();
}
